kostya13/kitchen-timer/schema/timer.sch

## KiCad design schema/timer.sch (2014-02-14, an earlier design)

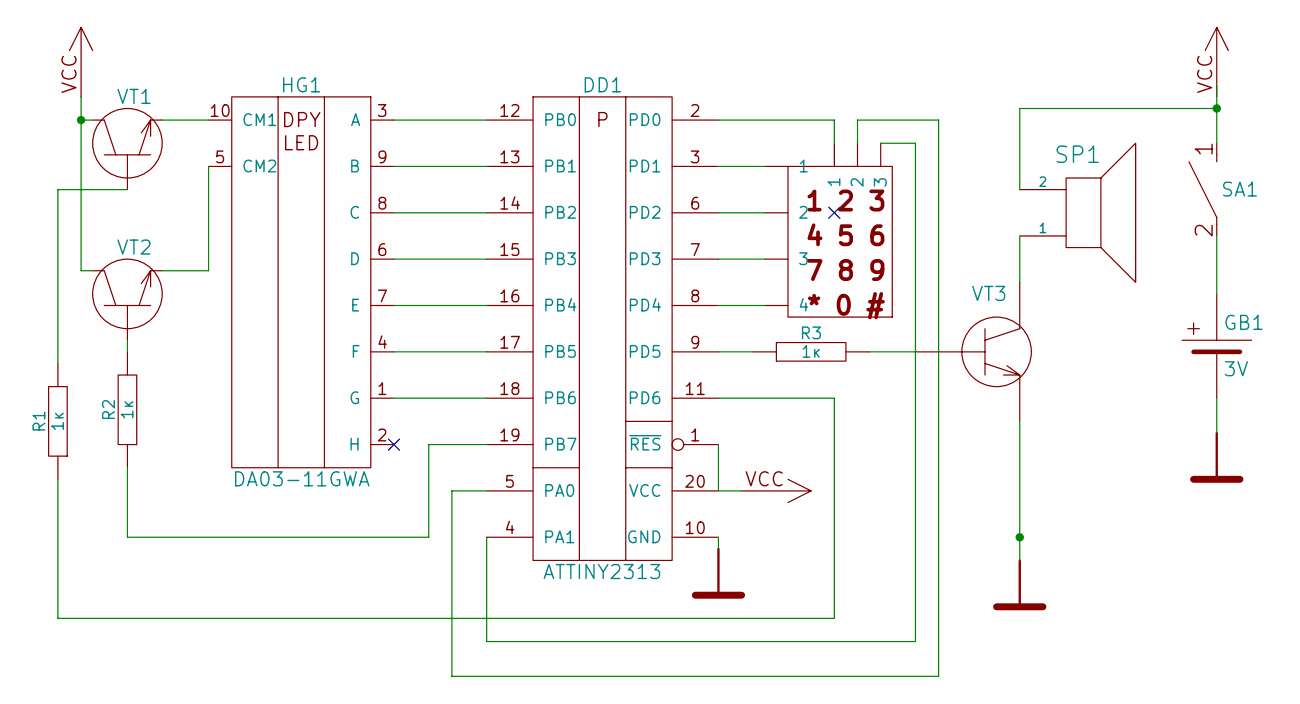
[picture p3: schematic timer.sch]

Parts:
DD1: ATTINY2313
GB1: 3V
HG1: DA03-11GWA
Kbd1: KEYBOARD
R1, R2, R3: 1к
SA1: SA_1-2_CL
SP1: SPEAKER
VT1, VT2: VT_NPN_BCE
VT3: TR_NPN_BCE

Connections:
unnamed: DD1.2 (PD0), Kbd1.~
unnamed: DD1.3 (PD1), Kbd1.~
unnamed: DD1.4 (PA1), Kbd1.~
unnamed: DD1.5 (PA0), Kbd1.~
unnamed: DD1.6 (PD2), Kbd1.~
unnamed: DD1.7 (PD3), Kbd1.~
unnamed: DD1.8 (PD4), Kbd1.~
unnamed: DD1.9 (PD5), R3.1
unnamed: DD1.11 (PD6), R1.1
unnamed: DD1.12 (PB0), HG1.3 (A)
unnamed: DD1.13 (PB1), HG1.9 (B)
unnamed: DD1.14 (PB2), HG1.8 (C)
unnamed: DD1.15 (PB3), HG1.6 (D)
unnamed: DD1.16 (PB4), HG1.7 (E)
unnamed: DD1.17 (PB5), HG1.4 (F)
unnamed: DD1.18 (PB6), HG1.1 (G)
unnamed: DD1.19 (PB7), R2.1
unnamed: GB1.1 (+), SA1.2
unnamed: HG1.5 (CM2), VT2.3 (E)
unnamed: HG1.10 (CM1), VT1.3 (E)
unnamed: R1.2, VT1.1 (B)
unnamed: R2.2, VT2.1 (B)
unnamed: R3.2, VT3.1 (B)
unnamed: SP1.1, VT3.2 (C)
POWER_GND: DD1.10 (GND), GB1.2 (-), VT3.3 (E)
POWER_VCC: DD1.1 (~RES), DD1.20 (VCC), SA1.1, SP1.2, VT1.2 (C), VT2.2 (C)
